bootsector/LLAMA/firmware/Input/Pads/Genesis_In.c

/*
* LLAMA - Low Lag Amazing MiSTer Adapter
*
* Copyright (c) 2019
* Bruno Freitas - bruno@brunofreitas.com - http://www.brunofreitas.com/
*
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
* You should have received a copy of the GNU General Public License
* along with this program. If not, see <http://www.gnu.org/licenses/>.
*/

#include <avr/io.h>
#include <util/delay.h>

#include "Genesis_In.h"
#include "Util.h"

#define DELAY 14

uint8_t Genesis_In_Init(void) {
	// DB9P1
	bit_clear(DDRF, 1 << 6);
	bit_set(PORTF, 1 << 6);

	// DB9P2
	bit_clear(DDRF, 1 << 0);
	bit_set(PORTF, 1 << 0);

	// DB9P3
	bit_clear(DDRF, 1 << 1);
	bit_set(PORTF, 1 << 1);

	// DB9P4
	bit_clear(DDRF, 1 << 4);
	bit_set(PORTF, 1 << 4);

	// DB9P6
	bit_clear(DDRF, 1 << 5);
	bit_set(PORTF, 1 << 5);

	// DB9P7
	bit_set(DDRE, 1 << 6);
	bit_set(PORTE, 1 << 6);

	// DB9P9
	bit_clear(DDRC, 1 << 7);
	bit_set(PORTC, 1 << 7);

	return 1;
}

static uint16_t genesis_read(void) {
	uint16_t retval;

	int extrabuttons = 0;
	int normalbuttons = 0;

	// Get D-PAD, B, C buttons state
	bit_set(PORTE, 1 << 6);
	_delay_us(DELAY);

	normalbuttons |= (!bit_check(PINF, 6) << 0);
	normalbuttons |= (!bit_check(PINF, 0) << 1);
	normalbuttons |= (!bit_check(PINF, 1) << 2);
	normalbuttons |= (!bit_check(PINF, 4) << 3);
	normalbuttons |= (!bit_check(PINF, 5) << 4);
	normalbuttons |= (!bit_check(PINC, 7) << 5);

	bit_clear(PORTE, 1 << 6);
	_delay_us(DELAY);

	// Is using a SEGA Genesis controller, LEFT and RIGHT will be ACTIVE here
	if(!(!bit_check(PINF, 1) && !bit_check(PINF, 4))) {
		retval = normalbuttons | (extrabuttons << 8);
		return retval;
	}

	// Get A and START buttons state
	normalbuttons |= (!bit_check(PINF, 5) << 6);
	normalbuttons |= (!bit_check(PINC, 7) << 7);

	bit_set(PORTE, 1 << 6);
	_delay_us(DELAY);
	bit_clear(PORTE, 1 << 6);
	_delay_us(DELAY);

	// Up, Down, Left and Right are low if 6-button controller
	if(!bit_check(PINF, 6) && !bit_check(PINF, 0) && !bit_check(PINF, 1) && !bit_check(PINF, 4)) {
		bit_set(PORTE, 1 << 6);
		_delay_us(DELAY);

		extrabuttons |= (!bit_check(PINF, 6) << 0);
		extrabuttons |= (!bit_check(PINF, 0) << 1);
		extrabuttons |= (!bit_check(PINF, 1) << 2);
		extrabuttons |= (!bit_check(PINF, 4) << 3);

		bit_clear(PORTE, 1 << 6);
		_delay_us(DELAY);

		// 8bitdo sega genesis receiver support - home button might be pressed here
		extrabuttons |= ((!bit_check(PINF, 6)) << 4);

		bit_set(PORTE, 1 << 6);
		_delay_us(DELAY);
		bit_clear(PORTE, 1 << 6);

		// Delay needed for settling joystick down
		_delay_ms(2);
	}

	retval = normalbuttons | (extrabuttons << 8);

	return retval;
}

void Genesis_In_GetPadState(AbstractPad_t *padData) {
	int button_data = genesis_read();

	padData->d_up = bit_check(button_data, GENESIS_UP);
	padData->d_down = bit_check(button_data, GENESIS_DOWN);
	padData->d_left = bit_check(button_data, GENESIS_LEFT);
	padData->d_right = bit_check(button_data, GENESIS_RIGHT);

	padData->x = bit_check(button_data, GENESIS_A);
	padData->a = bit_check(button_data, GENESIS_B);
	padData->b = bit_check(button_data, GENESIS_C);
	padData->lb = bit_check(button_data, GENESIS_X);
	padData->rb = bit_check(button_data, GENESIS_Z);
	padData->y = bit_check(button_data, GENESIS_Y);
	padData->start = bit_check(button_data, GENESIS_START);
	padData->back = bit_check(button_data, GENESIS_MODE);

	padData->menu = ((padData->d_up && padData->start) || bit_check(button_data, GENESIS_8BITDO_HOME));
}
